nlohr1/RasPi-automated-On-Off-circuit/Bild2.png

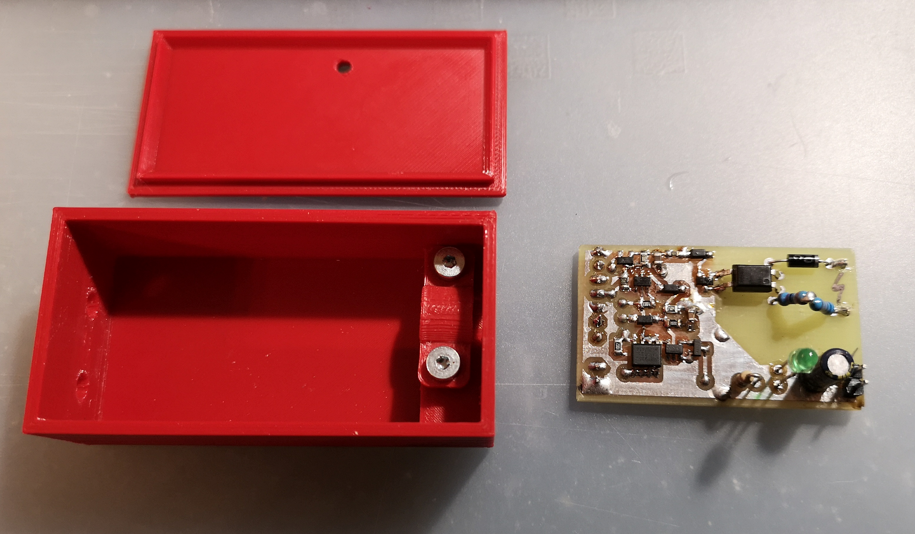
Bild2.png
