nlohr1/RasPi-automated-On-Off-circuit/Bild6.png

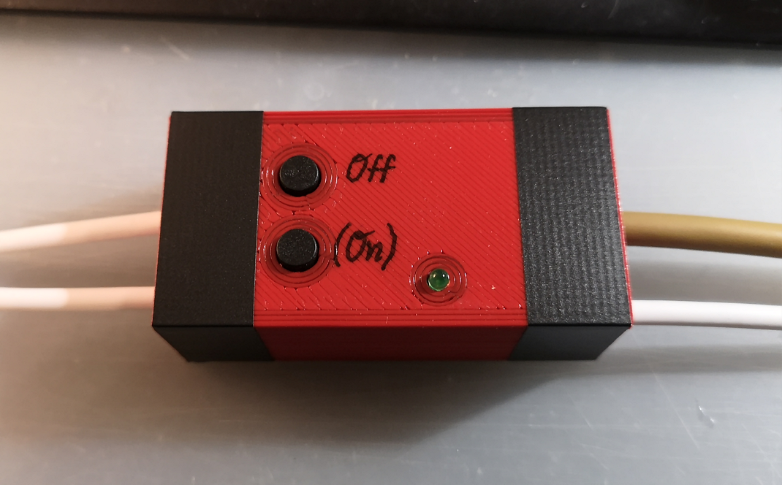
Bild6.png
