nlohr1/RasPi-automated-On-Off-circuit/GPIO-Connection-Cable.png

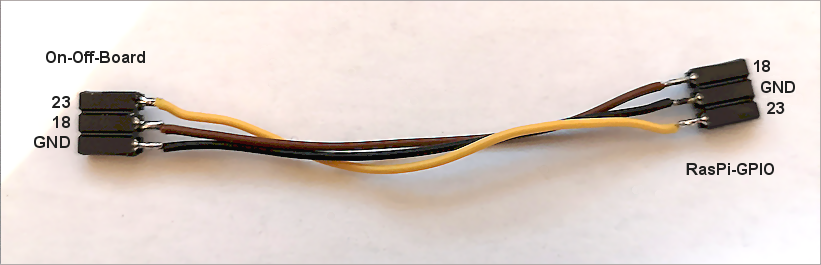
GPIO-Connection-Cable.png
