nlohr1/RasPi-automated-On-Off-circuit/Raspi-On-Off_Case.png

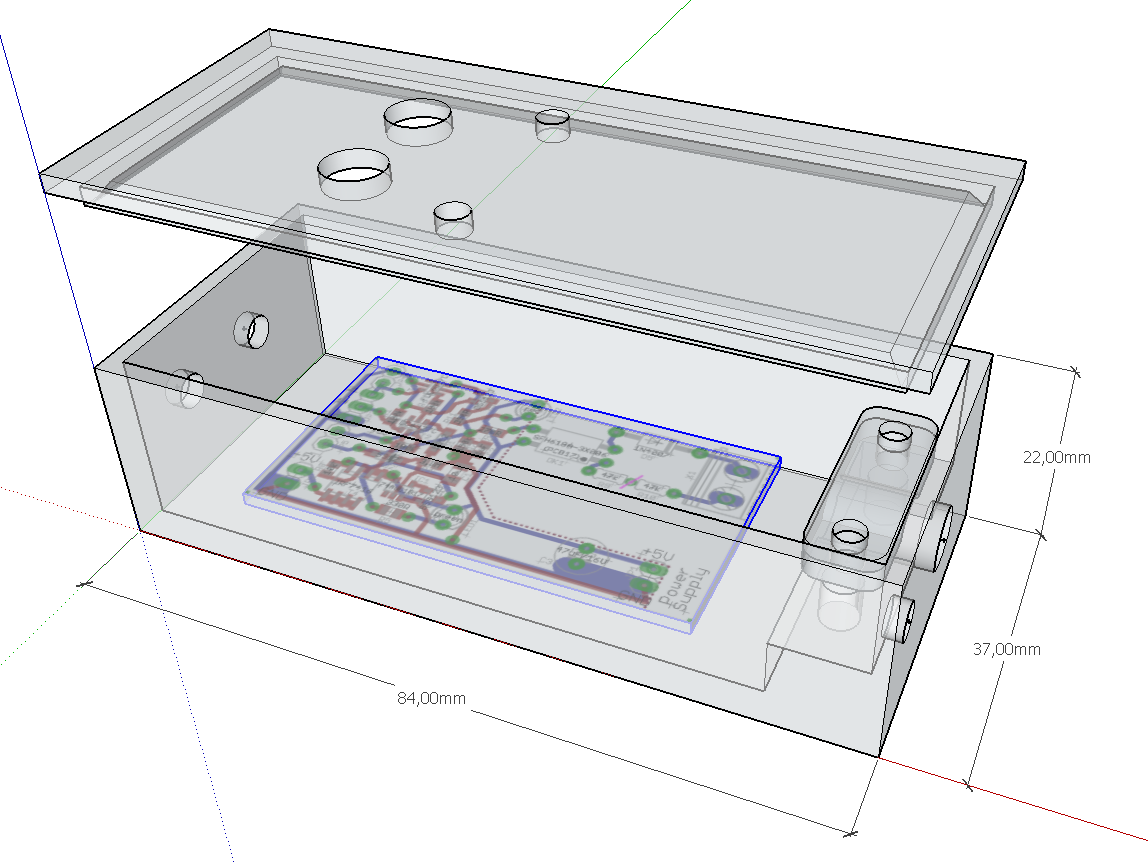
Raspi-On-Off_Case.png
