nlohr1/RasPi-automated-On-Off-circuit/Raspi-On-Off_Platform.png

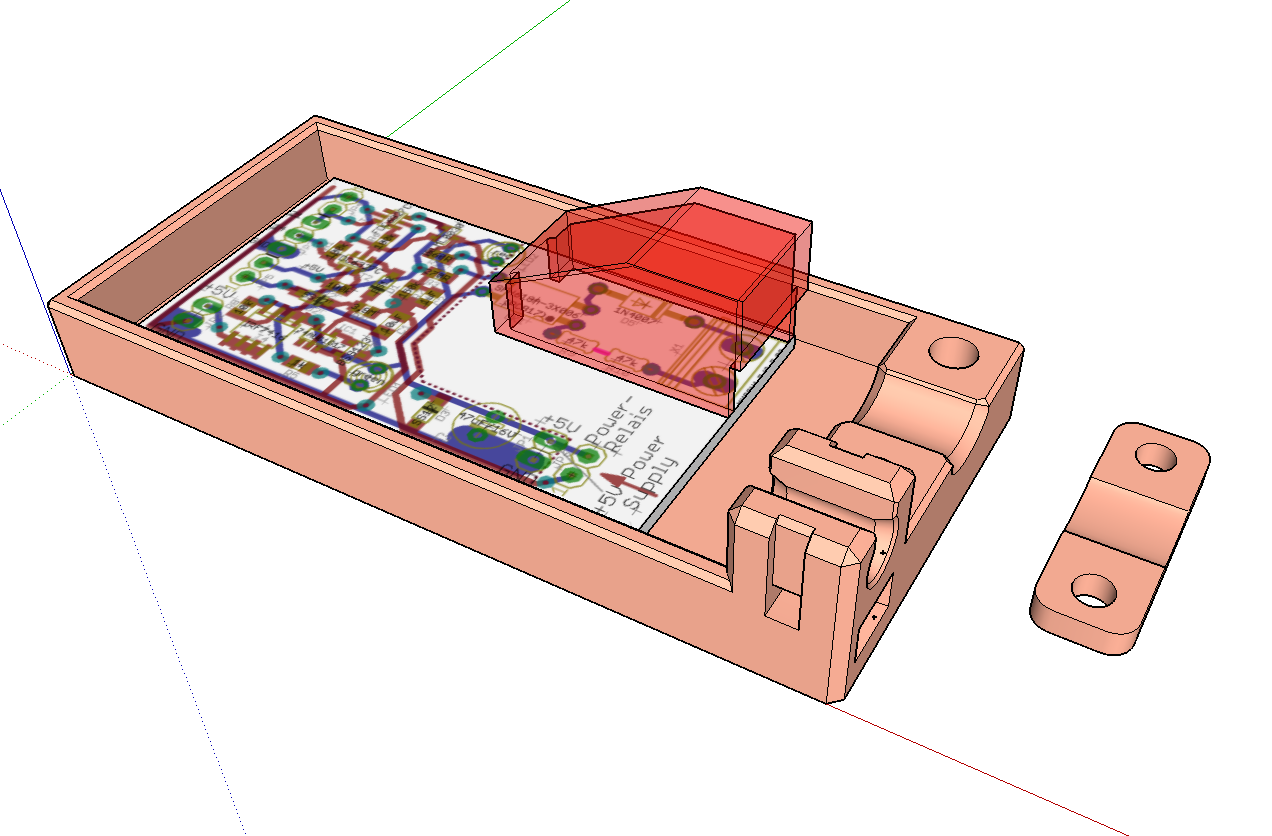
Raspi-On-Off_Platform.png
